furbrain/SAP5/enclosures/end_panel.fcstd

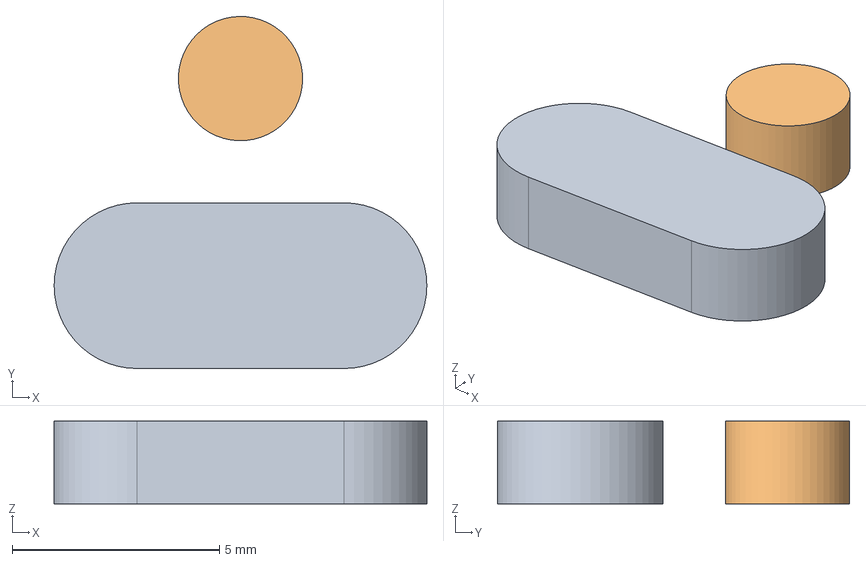
[picture p17: CAD file, 2019-11-15]
enclosures/end_panel.fcstd
9.00 x 8.50 x 2.00 mm
