furbrain/SAP5/enclosures/end_panel_create.dxf

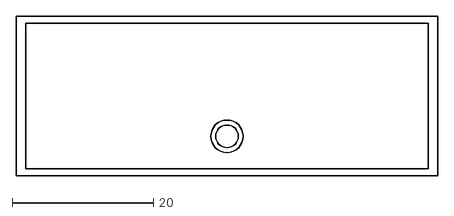
[picture p18: CAD file, 2019-04-08]
enclosures/end_panel_create.dxf
59.6 x 22.6
