furbrain/SAP5/enclosures/rangefinder.stp

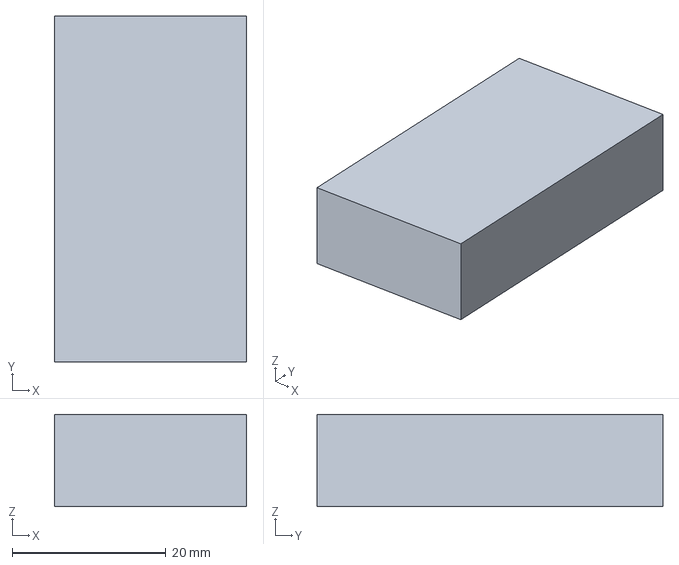
[picture p19: CAD file, 2018-06-10]
enclosures/rangefinder.stp
25.0 x 45.0 x 12.0 mm
