furbrain/SAP5/enclosures/boxl.fcstd

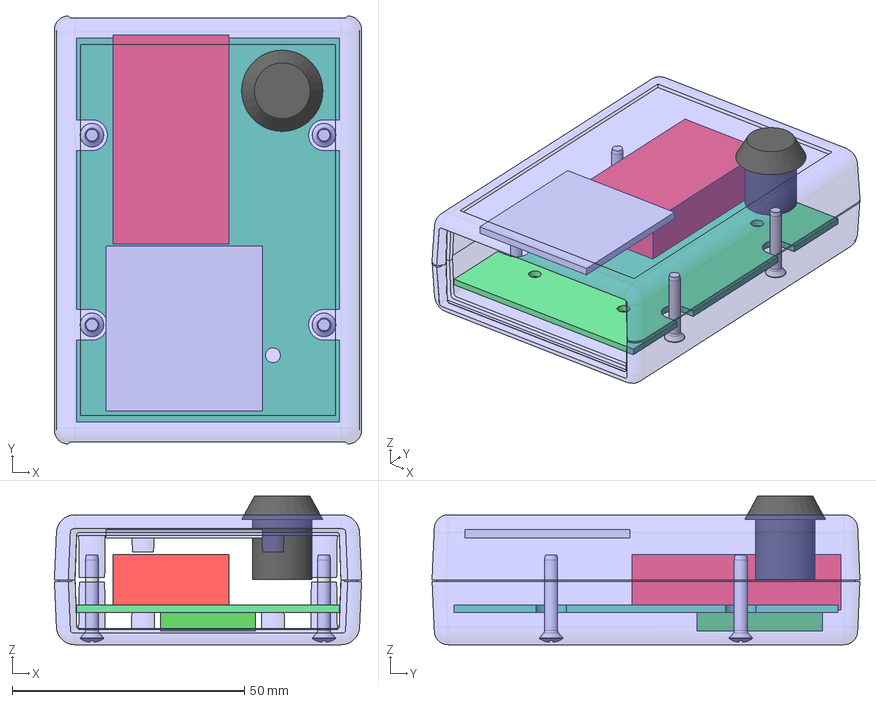
[picture p20: CAD file, 2018-06-10]
enclosures/boxl.fcstd
66.2 x 92.2 x 32.0 mm
1593L BOTTOM
1593L Top
1593L PCB
SC549 (screw #4X 3_4' OH)
SC549 (screw #4X 3_4' OH)001
SC549 (screw #4X 3_4' OH)002
SC549 (screw #4X 3_4' OH)003
Rangefinder
Battery
Button
