furbrain/SAP5/enclosures/button.fcstd

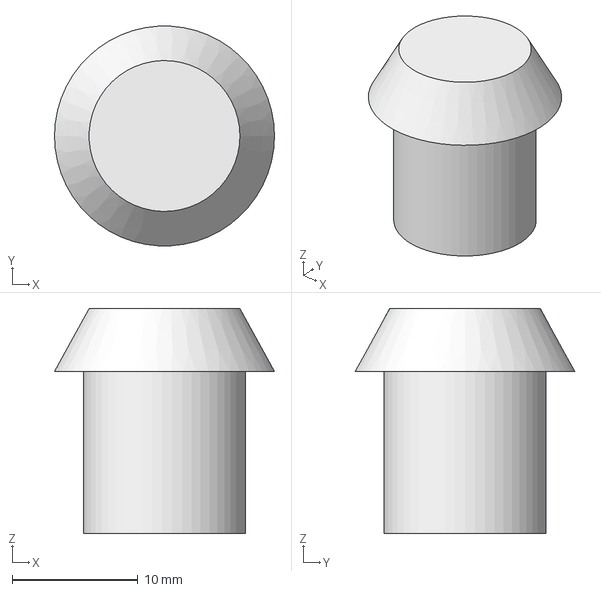
[picture p21: CAD file, 2018-06-10]
enclosures/button.fcstd
17.5 x 17.5 x 17.9 mm
