furbrain/SAP5/enclosures/box.fcstd

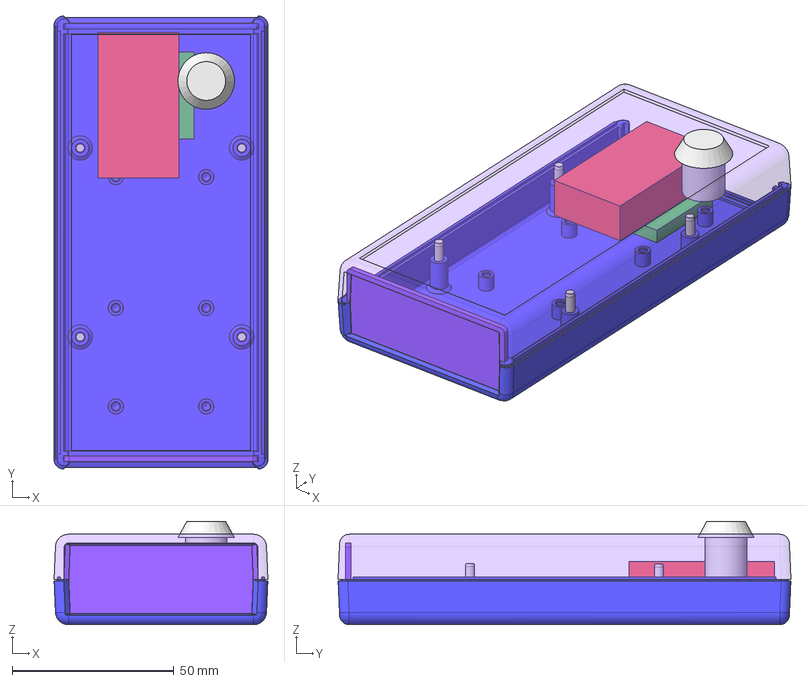
[picture p22: CAD file, 2018-06-10]
enclosures/box.fcstd
66.2 x 140.2 x 32.0 mm
1593X Bot
1593X Top
1593K-L-P-Q-X-Y Flat endplate
1593K-L-P-Q-X-Y Flat endplate001
SC549 (screw #4X 3_4' OH)
SC549 (screw #4X 3_4' OH)001
SC549 (screw #4X 3_4' OH)002
SC549 (screw #4X 3_4' OH)003
Rangefinder
Battery
