furbrain/SAP5/firmware/version.h

/* 
 * File:   version.h
 * Author: phil
 *
 * Created on 29 January 2020, 20:44
 */

#ifndef VERSION_H
#define	VERSION_H

#ifdef	__cplusplus
extern "C" {
#endif

#include <stdint.h>
//Version 1.2.0
#define VERSION_MAJOR 1
#define VERSION_MINOR 2
#define VERSION_REVISION 3

#define VERSION_CONFIG 2
#define VERSION_LEG 1
#define VERSION_CALIBRATION 1

enum HARDWARE_VERSION {
    VERSION_ALPHA,
    VERSION_V1_0,
    VERSION_V1_1,
    VERSION_UNDEFINED = 0xff
};    
    
extern enum HARDWARE_VERSION version_hardware;

struct SOFTWARE_VERSION {
    struct {
        uint8_t major;
        uint8_t minor;
        uint8_t revision;
        uint8_t checksum;
    } version;
    struct {
        uint32_t location;
        uint16_t size;
        uint8_t version;
    } config;
    struct {
        uint32_t location;
        uint16_t size;
        uint8_t version;
    } legs;
    struct {
        uint32_t location;
        uint16_t size;
        uint8_t version;
    } calibration;
};

extern struct SOFTWARE_VERSION version_software;

// Identify the hardware version this code is running on
void find_version(void);


struct VERSION_ID {
   const char *adjective;
   const char *animal;
};

struct VERSION_ID version_get_id(void);

uint8_t version_get_case_length(void);
#ifdef	__cplusplus
}
#endif

#endif	/* VERSION_H */
