furbrain/SAP5/bt_code/src/gatt_db.h

#ifndef _GATT_DB_H_
#define _GATT_DB_H_
#include <stdbool.h>

tBleStatus Add_Chat_Service(void);
void Attribute_Modified_CB(uint16_t handle, uint16_t data_length, uint8_t *att_data);
const char* get_bt_text(void);

extern uint16_t chatServHandle, TXCharHandle, RXCharHandle;

#endif /* _GATT_DB_H_ */
