furbrain/SAP5/test/test/make_test_cases.py

#!/usr/bin/python

import numpy as np
import scipy.linalg
import quaternion
import re
import random
import matplotlib.pyplot as plt
from mpl_toolkits.mplot3d import Axes3D

def bracketiser(arr):
    arr = str(arr).replace('  ',' ')
    arr = arr.replace('  ',' ')
    arr = arr.replace('  ',' ')
    arr = arr.replace('  ',' ')
    arr = arr.replace('[ ','[')    
    arr = arr.replace(' ]',']')    
    arr = arr.replace('[','{')
    arr = arr.replace(']]','}]')
    arr = arr.replace(']','},')
    arr = re.sub('([0123456789\.]) ','\\1,', arr)
    arr = arr.replace('\n','')
    arr = arr.replace(',}','}')
    arr = re.sub(',$','',arr)
    return arr
    
def get_random_matrix(scale=2):
    m = (np.random.random((4,4))*scale*2)-scale
    m[3][0:3] = 0
    m[3][3] = 1
    return m

def get_random_vector():
    v = (np.random.random(4)*4)-2
    v[3] = 1
    return v
    
def to_points(x):
    return [math.sin(x)*SCALE, math.cos(x)*SCALE]
    
def get_2d_rotation_matrix(theta):
    c, s = np.cos(theta), np.sin(theta)
    return np.matrix([[c, s], [-s, c]])

def create_2d_raw_data(sample_count, theta, offset, noise=0, scale=10, skew=1.2):
    angles = np.random.random(sample_count)*np.pi*2
    points = np.array([np.sin(angles)*scale, np.cos(angles)*scale]).T
    points += np.random.random((sample_count,2))*noise-(noise/2)
    mat = create_2d_rotation_and_scale_matrix(theta, skew)
    points = np.matmul(points, mat)
    points += offset
    return points

def create_2d_rotation_and_scale_matrix(theta, skew):
    rot_mat = get_2d_rotation_matrix(theta)
    scale_mat = np.matrix([[skew,0], [0,1]])
    return np.matmul(np.matmul(np.linalg.inv(rot_mat), scale_mat), rot_mat)


def make_rotation_matrix(theta, axes):
    m = np.identity(4)
    c,s = (np.cos(theta), np.sin(theta))
    a,b = axes[0],axes[1]
    m[a][a] = c
    m[a][b] = s
    m[b][a] = -s
    m[b][b] = c
    return m
    
def make_scale_matrix(scale, axis):
    m = np.identity(4)
    m[axis][axis] = scale
    return m

def make_2d_rotation_fixture():
    axes = np.arange(3)
    for i in range(10):
        if (i==0):
            calib = np.identity(4)
            calib[0][3]=2
            calib[1][3]=3
            theta = np.pi/2
        else:
            calib = get_random_matrix()
            theta = np.random.random() *2 *np.pi
        vec = (np.cos(theta), np.sin(theta))
        np.random.shuffle(axes)
        original = calib.copy();
        calib = np.matmul(make_rotation_matrix(theta, axes[0:2]), calib)
        print "{%s, %s, %s,  %s}," % (bracketiser(axes[0:2]), bracketiser(vec), bracketiser(original[0:3]), bracketiser(calib[0:3]))
        
def make_scale_fixture():
    axes = np.arange(3)
    for i in range(10):
        if (i==0):
            calib = np.identity(4)
            calib[0][3]=2
            calib[1][3]=3
            scale = 3
        else:
            calib = get_random_matrix()
            scale = np.random.random()*4-2
        axis = np.random.randint(3)
        original = calib.copy();
        calib = np.matmul(make_scale_matrix(scale, axis), calib)
        print "{%d, %f, %s,  %s}," % (axis, scale, bracketiser(original[0:3]), bracketiser(calib[0:3]))

def make_multiply_matrices_fixture():
    for k in range(2):
        calib = np.identity(4)
        for i in range(5):
            delta = get_random_matrix(1.0)
            calib = np.matmul(delta, calib)
            print "{%s, %s}," % (bracketiser(delta[0:3]), bracketiser(calib[0:3]))
            
def make_get_orientation_fixture():
    for i in range(10):
        if (i==0):
            accel = np.array([0,0,-1.0])
            mag = np.array([0,6,-8])
        elif (i==1):
            accel = np.array([0,0,-1.0])
            mag = np.array([-6,0,-8])
        elif (i==2):
            accel = np.array([0,1.0,0])
            mag = np.array([-6,8,0])
        else:
            accel = get_random_vector()[:3]
            mag = get_random_vector()[:3]
        accel_normed = accel / np.linalg.norm(accel)
        east = np.cross(accel, mag)
        east /= np.linalg.norm(east)
        north = np.cross(east, accel)
        north /= np.linalg.norm(north)
        orientation = np.array([0.0,0.0,0.0])
        orientation[0] = east[1]
        orientation[1] = north[1]
        orientation[2] = -accel_normed[1]
        orientation /= np.linalg.norm(orientation)
        print "{%s, %s, %s}," % (bracketiser(accel), bracketiser(mag), bracketiser(orientation))
            
def make_normalise_fixture():
    for i in range(10):
        vector = get_random_vector()[:3]
        original = vector.copy()
        vector /= np.linalg.norm(vector)
        print "{%s, %s}," % (bracketiser(original), bracketiser(vector))
            
def make_find_rotation_and_scale_fixture(samples, skew=1.2, noise=0):
    theta = np.random.random()*np.pi
    points = create_2d_raw_data(samples, theta, [0,0])
    vectors = np.zeros((samples,3))
    axes = np.arange(3)
    np.random.shuffle(axes)
    a = int(axes[0])
    b = int(axes[1])
    vectors[:, a:a+1] = points[:, 0]
    vectors[:, b:b+1] = points[:, 1]
    print theta
    print skew
    print axes
    print bracketiser(vectors)
    
def make_find_plane_fixtures(samples):
    noise = 0.1
    orientation  = np.quaternion(1,0,0,0)
    orientation *= np.exp(quaternion.x * random.random()* 0.1 / 2) 
    orientation *= np.exp(quaternion.y* random.random()* 0.1 / 2)
    points = create_2d_raw_data(samples, offset = [0,0], theta=0, skew=1.0)
    vectors = np.full((samples,3),-10.0)
    vectors[:, 0:2] = points
    vectors += np.random.random((samples, 3))*noise-(noise/2)
    vectors = np.append(vectors,[[0, 0, -1]], axis=0)
    vectors = quaternion.rotate_vectors(orientation, vectors)
    axes = np.arange(3)
    np.random.shuffle(axes)
    i = np.argsort(axes)
    vectors = vectors[:,i]
    print bracketiser(vectors[:-1,:])
    print bracketiser(axes[:2])
    print bracketiser(vectors[-1:,:])    

def make_sqrtm_fixtures():
    for i in range(5):
        b = np.random.random((3,3))
        b_symm = (b + b.T)/2 +3*np.eye(3)
        print bracketiser(b_symm),',', bracketiser(scipy.linalg.sqrtm(b_symm))    

def make_convert_to_device_fixtures(samples):
    np.random.seed(56)
    orientation  = np.quaternion(1,0,0,0)
    orientation *= np.exp(quaternion.x * np.random.random()) 
    orientation *= np.exp(quaternion.y* np.random.random())
    print bracketiser(quaternion.as_rotation_matrix(orientation))
    for i in range(samples):
        vector = np.random.random((3,))
        res = quaternion.rotate_vectors(orientation, vector)
        print '{',bracketiser(vector), ',', bracketiser(list(reversed(-1*res[0:2]))),'},'
        
def make_apply_calibration_fixtures(samples):
    for i in range(samples):
        src = get_random_vector()[:3]
        trans = get_random_matrix()[:3,:3]
        offset = get_random_vector()[:3]
        result = np.dot(trans,src+offset)
        print '{' + ','.join(bracketiser(x) for x in (src, trans, offset, result)) + '},'
        
def make_plane_to_rotation_fixtures(samples):
    for i in range(samples):
        orientation  = np.quaternion(1,0,0,0)
        orientation *= np.exp(quaternion.x * np.random.uniform(-0.1,0.1))
        orientation *= np.exp(quaternion.z * np.random.uniform(-0.1,0.1)) 
        z = quaternion.rotate_vectors(orientation,[0,1,0])
        if random.choice([True,False]):
            z *= -1
        print bracketiser(z),','

np.set_printoptions(suppress=True, precision=4)
np.random.seed(10)

make_plane_to_rotation_fixtures(20)
