furbrain/SAP5/firmware/i2c_util.h

/* I2C utility funcs*/
#ifndef I2C_UTIL_H
#define I2C_UTIL_H
#include "app_type.h"
#include <stdint.h>

#define EEPROM_ADDRESS 0x50
#define I2C_FAST 37
#define I2C_STANDARD 200

typedef struct {
    uint8_t reg;
    uint8_t value;    
} i2c_multi_commands;

int8_t write_i2c_block(uint8_t address, uint8_t *data, uint8_t length);

int8_t read_i2c_block(uint8_t address, uint8_t *data, uint8_t length);

int8_t write_i2c_command_block(uint8_t address, uint8_t command, const uint8_t *data, uint8_t length);

int8_t write_i2c_data2(uint8_t address, uint8_t command, uint8_t data);

int8_t read_eeprom_data(uint16_t address, uint8_t *data, uint8_t length);
int8_t write_i2c_data1(uint8_t address, uint8_t command);
#ifndef BOOTLOADER




int8_t read_i2c_data(uint8_t address, uint8_t command, uint8_t *data, uint8_t length);

int8_t write_eeprom_data(uint16_t address, const uint8_t *data, uint8_t length);

bool check_i2c_address(uint8_t address);

void write_i2c_multi(uint8_t address, const i2c_multi_commands *commands, uint8_t length);

#endif
#endif
